olell/dezentrale-badge/Firmware/include/funconfig.h

#ifndef _FUNCONFIG_H
#define _FUNCONFIG_H

#define FUNCONF_USE_HSI 1    		// internal 24MHz clock oscillator
#define FUNCONF_USE_PLL 1			// use PLL x2
#define RANDOM_STRENGTH    2
#define FUNCONF_SYSTICK_USE_HCLK 1
#define CH32V003           1

#endif
